MbFredys/PCB-Modular-Multi-Protocol-Hub/Manufacturing/3rd Layer.png

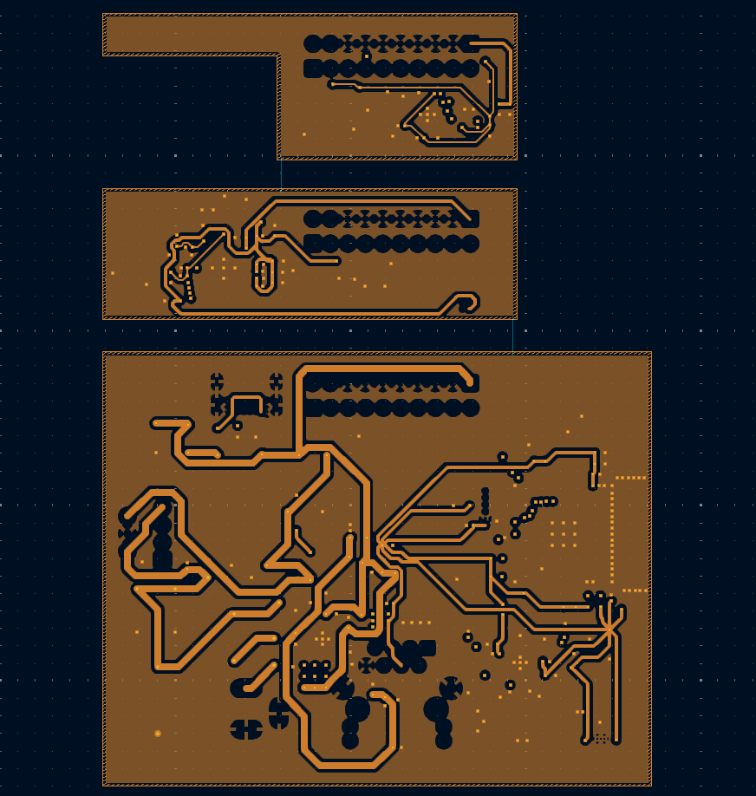
Manufacturing/3rd Layer.png
