MbFredys/PCB-Modular-Multi-Protocol-Hub/Manufacturing/Bottom Layer.png

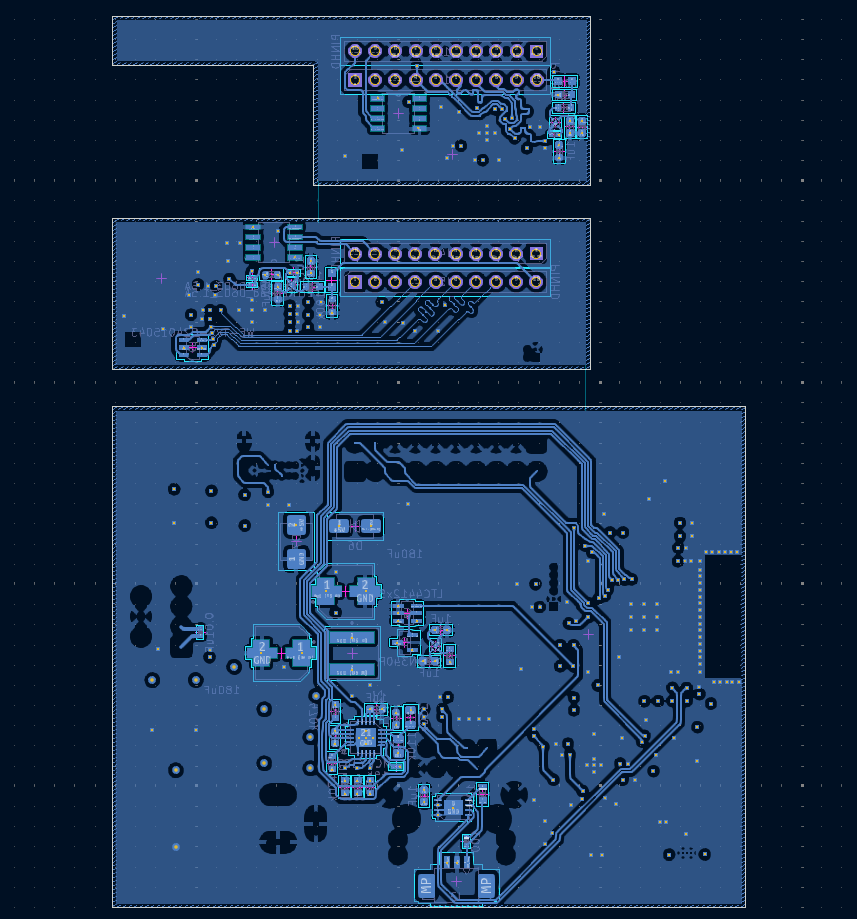
Manufacturing/Bottom Layer.png
