MbFredys/PCB-Modular-Multi-Protocol-Hub/Manufacturing/Top Layer.png

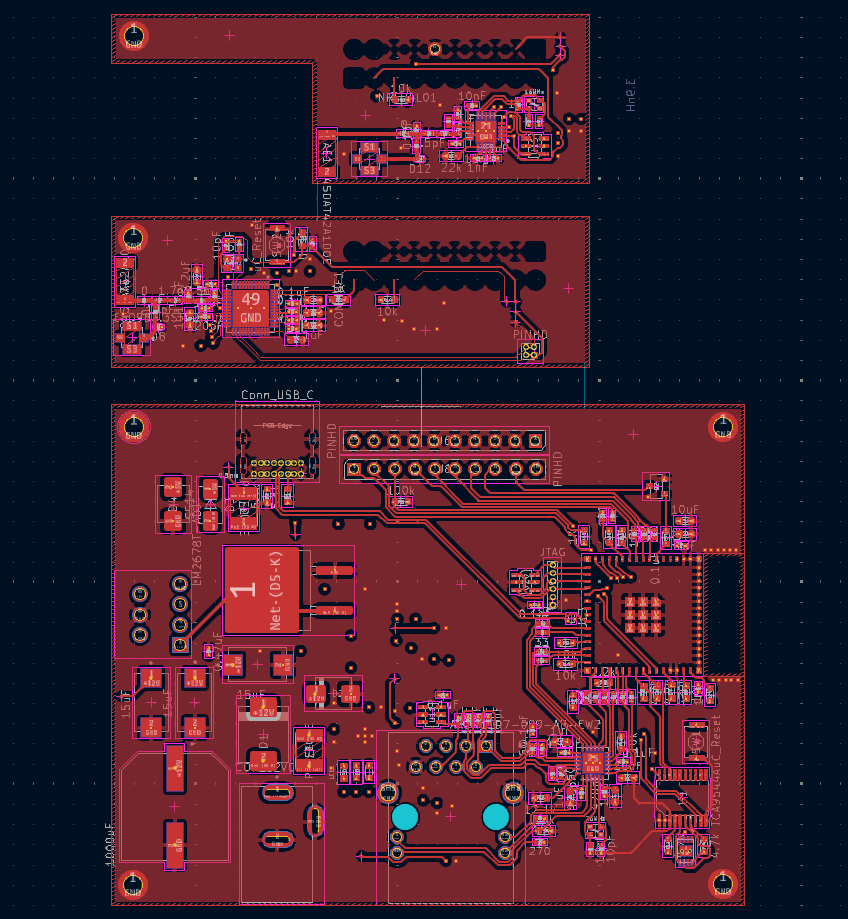
Manufacturing/Top Layer.png
